galatas123/Measurement_Stations/3D printed Housing/cad/top_v1.FCStd

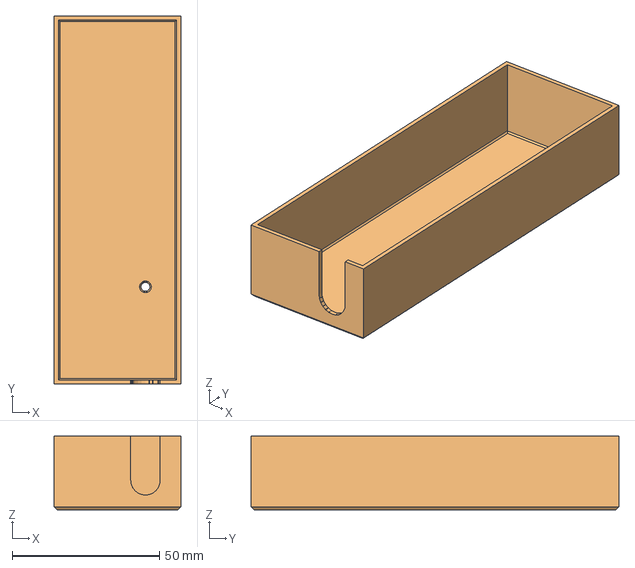
[picture p22: CAD file, 2023-07-07, an earlier design]
3D printed Housing/cad/top_v1.FCStd
43.0 x 125.0 x 25.0 mm
Body (Meshed)
