galatas123/Measurement_Stations/3D printed Housing/cad/top_v4.FCStd

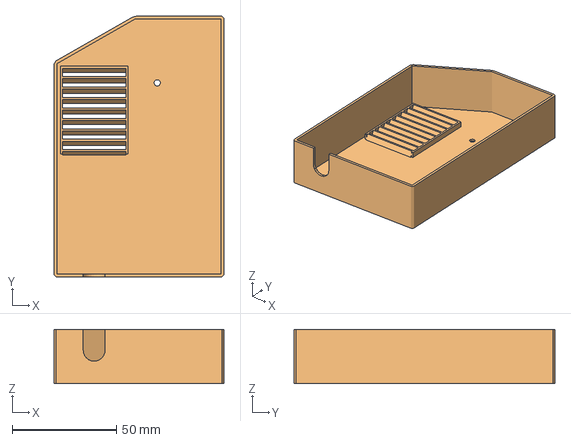
[picture p23: CAD file, 2023-07-07, an earlier design]
3D printed Housing/cad/top_v4.FCStd
81.5 x 125.0 x 26.0 mm
Pocket003 (Meshed)
